Prime9999/MZ80K_SD_Pico2/KiCad/MZ80K_SD_Pico2.kicad_sch

## KiCad design KiCad/MZ80K_SD_Pico2.kicad_sch (2024-10-17)

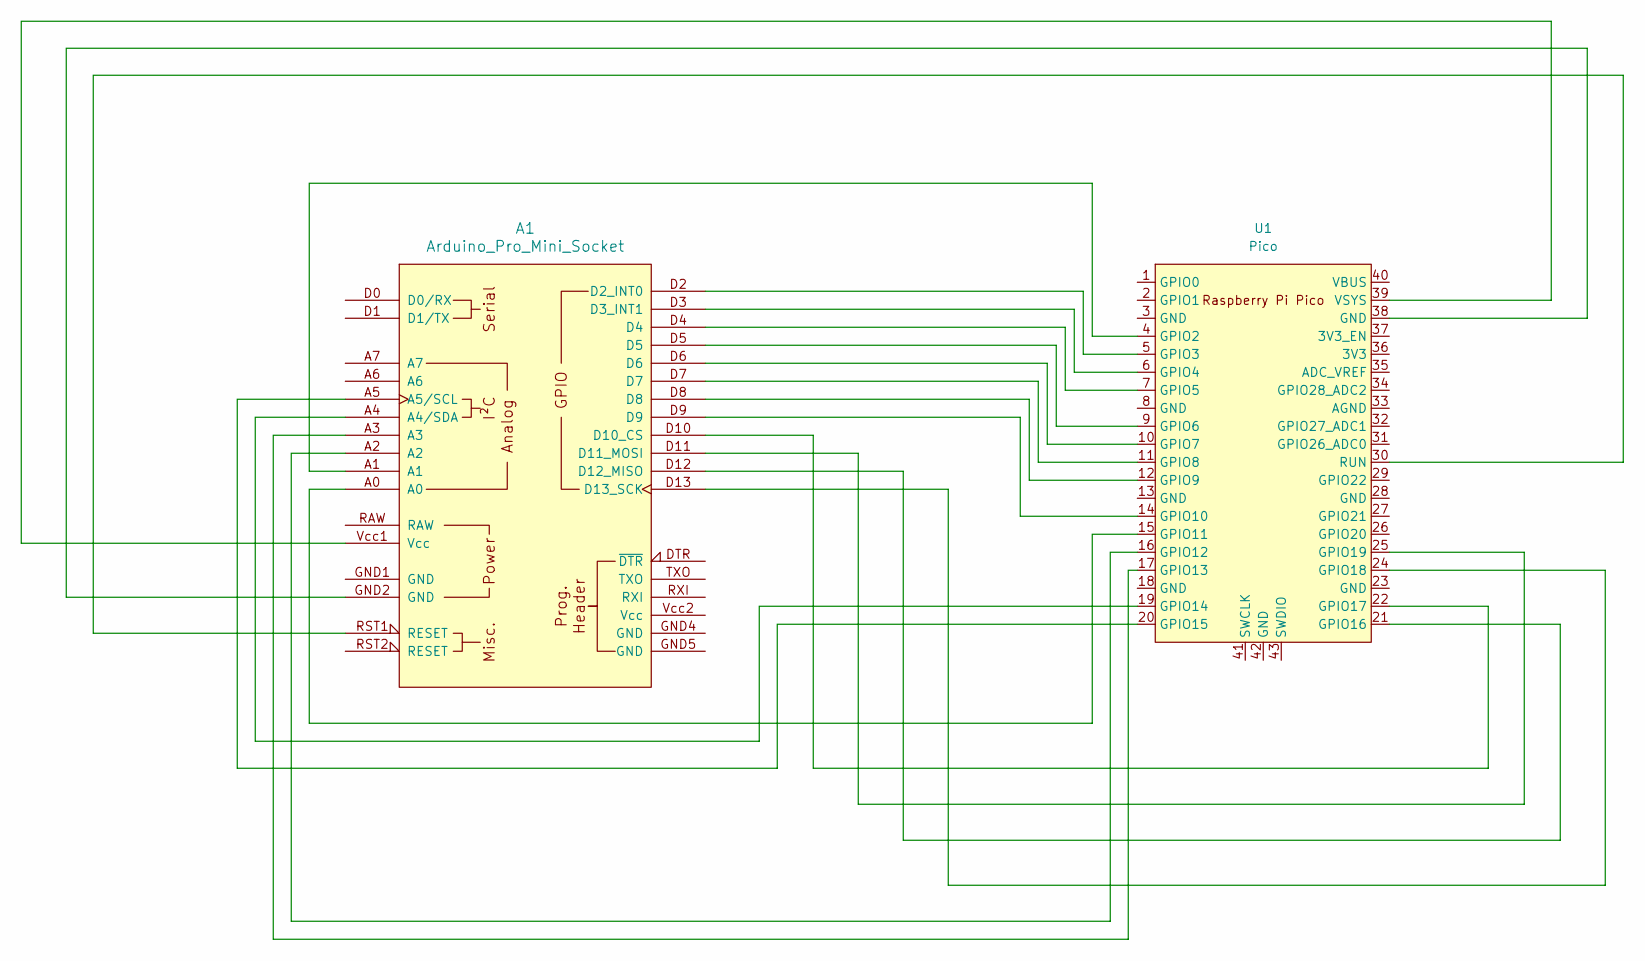
[picture p2: schematic MZ80K_SD_Pico2.kicad_sch]

Parts:
A1: Arduino_Pro_Mini_Socket; Arduino_Pro_Mini_Socket_NoSPH_2
U1: Pico; RPi_Pico_SMD_TH_2

Connections:
unnamed: A1.A0, U1.15 (GPIO11)
unnamed: A1.A1, U1.4 (GPIO2)
unnamed: A1.A2, U1.16 (GPIO12)
unnamed: A1.A3, U1.17 (GPIO13)
unnamed: A1.A4 (A4/SDA), U1.19 (GPIO14)
unnamed: A1.A5 (A5/SCL), U1.20 (GPIO15)
unnamed: A1.D2 (D2_INT0), U1.5 (GPIO3)
unnamed: A1.D3 (D3_INT1), U1.6 (GPIO4)
unnamed: A1.D4, U1.7 (GPIO5)
unnamed: A1.D5, U1.9 (GPIO6)
unnamed: A1.D6, U1.10 (GPIO7)
unnamed: A1.D7, U1.11 (GPIO8)
unnamed: A1.D8, U1.12 (GPIO9)
unnamed: A1.D9, U1.14 (GPIO10)
unnamed: A1.D10 (D10_CS), U1.22 (GPIO17)
unnamed: A1.D11 (D11_MOSI), U1.25 (GPIO19)
unnamed: A1.D12 (D12_MISO), U1.21 (GPIO16)
unnamed: A1.D13 (D13_SCK), U1.24 (GPIO18)
unnamed: A1.GND2 (GND), U1.38 (GND)
unnamed: A1.RST1 (RESET), U1.30 (RUN)
unnamed: A1.Vcc1 (Vcc), U1.39 (VSYS)
