Prime9999/MZ80K_SD_Pico2/Arduino/MZ-80K_SD_Pico2/char_table.h

/* MZ-700 Character code - UTF8 conversion table (0x70-) */

//#define SMALL_MODEL
#define MIN_ASCII_CODE ((uint8_t)0x70)
#ifdef SMALL_MODEL
#define MAX_ASCII_CODE ((uint8_t)0xbf)
#else
#define MAX_ASCII_CODE ((uint8_t)0xff)
#endif

typedef struct _ct {
  uint8_t len; // 0: cannot convert
  uint8_t bytes[3];
} char_table;

const char_table a_to_u[] PROGMEM = {
  {3, {0xe6, 0x97, 0xa5}}, // 0x70(日)
  {3, {0xe6, 0x9c, 0x88}}, // 0x71(月)
  {3, {0xe7, 0x81, 0xab}}, // 0x72(火)
  {3, {0xe6, 0xb0, 0xb4}}, // 0x73(水)
  {3, {0xe6, 0x9c, 0xA8}}, // 0x74(木)
  {3, {0xe9, 0x87, 0x91}}, // 0x75(金)
  {3, {0xe5, 0x9c, 0x9f}}, // 0x76(土)
  {3, {0xe7, 0x94, 0x9f}}, // 0x77(生)
  {3, {0xe5, 0xb9, 0xb4}}, // 0x78(年)
  {3, {0xe6, 0x99, 0x82}}, // 0x79(時)
  {3, {0xe5, 0x88, 0x86}}, // 0x7a(分)
  {3, {0xe7, 0xa7, 0x92}}, // 0x7b(秒)
  {3, {0xe5, 0x86, 0x86}}, // 0x7c(円)
  {0, {0x00, 0x00, 0x00}}, // 0x7d(￥)
  {3, {0xef, 0xbf, 0xa1}}, // 0x7e(￡)
  {0, {0x00, 0x00, 0x00}}, // 0x7f(PLAY)

  {0, {0x00, 0x00, 0x00}}, // 0x80(↓)
  {3, {0xef, 0xbd, 0xa1}}, // 0x81(｡)
  {3, {0xef, 0xbd, 0xa2}}, // 0x82(｢)
  {3, {0xef, 0xbd, 0xa3}}, // 0x83(｣)
  {3, {0xef, 0xbd, 0xa4}}, // 0x84(､)
  {3, {0xef, 0xbd, 0xa5}}, // 0x85(･)
  {3, {0xef, 0xbd, 0xa6}}, // 0x86(ｦ)
  {3, {0xef, 0xbd, 0xa7}}, // 0x87(ｧ)
  {3, {0xef, 0xbd, 0xa8}}, // 0x88(ｨ)
  {3, {0xef, 0xbd, 0xa9}}, // 0x89(ｩ)
  {3, {0xef, 0xbd, 0xaa}}, // 0x8a(ｪ)
  {3, {0xef, 0xbd, 0xab}}, // 0x8b(ｫ)
  {3, {0xef, 0xbd, 0xac}}, // 0x8c(ｬ)
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
  {3, {0xe2, 0x97, 0xa3}}, // 0xe9(◣)
  {3, {0xe2, 0x95, 0xb0}}, // 0xea(╰)
  {3, {0xe2, 0x95, 0xaf}}, // 0xeb(╯)
  {0, {0x00, 0x00, 0x00}}, // 0xec(??)
  {3, {0xe2, 0x95, 0xb2}}, // 0xed(╲)
  {3, {0xe2, 0x95, 0xb1}}, // 0xee(╱)
  {0, {0x00, 0x00, 0x00}}, // 0xef(??)

  {0, {0x00, 0x00, 0x00}}, // 0xf0(??)
  {3, {0xe2, 0x97, 0x8f}}, // 0xf1(●)
  {0, {0x00, 0x00, 0x00}}, // 0xf2(??)
  {3, {0xe2, 0x99, 0xa5}}, // 0xf3(♥)
  {0, {0x00, 0x00, 0x00}}, // 0xf4(??)
  {3, {0xe2, 0x97, 0xa2}}, // 0xf5(◢)
  {3, {0xe2, 0x95, 0xb3}}, // 0xf6(╳)
  {3, {0xe2, 0x97, 0x8b}}, // 0xf7(○)
  {3, {0xe2, 0x99, 0xa3}}, // 0xf8(♣)
  {0, {0x00, 0x00, 0x00}}, // 0xf9(??)
  {3, {0xe2, 0x99, 0xa6}}, // 0xfa(♦)
  {3, {0xe2, 0x94, 0xbc}}, // 0xfb(┼)
  {0, {0x00, 0x00, 0x00}}, // 0xfc(??)
  {3, {0xe2, 0x94, 0x82}}, // 0xfd(│)
  {3, {0xe2, 0x97, 0xa5}}, // 0xfe(◥)
  {2, {0xcf, 0x80, 0x00}}, // 0xff(π)
#endif
};
