Prime9999/MZ80K_SD_Pico2/Arduino/PC-8001_SD_Pico2/char_table.h

/* PC-8001 Character code - UTF8 conversion table (0x80-) */

#define MIN_ASCII_CODE ((uint8_t)0x80)
#define MAX_ASCII_CODE ((uint8_t)0xff)

typedef struct _ct {
  uint8_t len; // 0: cannot convert
  char bytes[3];
} char_table;

const char_table a_to_u[] PROGMEM = {
  {3, {0xe2, 0x96, 0x81}}, // 0x80(▁)
  {3, {0xe2, 0x96, 0x82}}, // 0x81(▂)
  {3, {0xe2, 0x96, 0x83}}, // 0x82(▃)
  {3, {0xe2, 0x96, 0x84}}, // 0x83(▄)
  {3, {0xe2, 0x96, 0x85}}, // 0x84(▅)
  {3, {0xe2, 0x96, 0x86}}, // 0x85(▆)
  {3, {0xe2, 0x96, 0x87}}, // 0x86(▇)
  {3, {0xe2, 0x96, 0x88}}, // 0x87(█)
  {3, {0xe2, 0x96, 0x8f}}, // 0x88(▏)
  {3, {0xe2, 0x96, 0x8e}}, // 0x89(▎)
  {3, {0xe2, 0x96, 0x8d}}, // 0x8a(▍)
  {3, {0xe2, 0x96, 0x8c}}, // 0x8b(▌)
  {3, {0xe2, 0x96, 0x8b}}, // 0x8c(▋)
  {3, {0xe2, 0x96, 0x8a}}, // 0x8d(▊)
  {3, {0xe2, 0x96, 0x89}}, // 0x8e(▉)
  {3, {0xe2, 0x94, 0xbc}}, // 0x8f(┼)

  {3, {0xe2, 0x94, 0xb4}}, // 0x90(┴)
  {3, {0xe2, 0x94, 0xac}}, // 0x91(┬)
  {3, {0xe2, 0x94, 0xa4}}, // 0x92(┤)
  {3, {0xe2, 0x94, 0x9c}}, // 0x93(├)
  {3, {0xe2, 0x96, 0x94}}, // 0x94(▔)
  {3, {0xe2, 0x94, 0x80}}, // 0x95(─)
  {3, {0xe2, 0x94, 0x82}}, // 0x96(│)
  {3, {0xe2, 0x96, 0x95}}, // 0x97(▕)
  {3, {0xe2, 0x94, 0x8c}}, // 0x98(┌)
  {3, {0xe2, 0x94, 0x90}}, // 0x99(┐)
  {3, {0xe2, 0x94, 0x94}}, // 0x9a(└)
  {3, {0xe2, 0x94, 0x98}}, // 0x9b(┘)
  {3, {0xe2, 0x95, 0xad}}, // 0x9c(╭)
  {3, {0xe2, 0x95, 0xae}}, // 0x9d(╮)
  {3, {0xe2, 0x95, 0xb0}}, // 0x9e(╰)
  {3, {0xe2, 0x95, 0xaf}}, // 0x9f(╯)

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
  {0, {0x00, 0x00, 0x00}}, // 0xf9()
  {0, {0x00, 0x00, 0x00}}, // 0xfa()
  {0, {0x00, 0x00, 0x00}}, // 0xfb()
  {0, {0x00, 0x00, 0x00}}, // 0xfc()
  {0, {0x00, 0x00, 0x00}}, // 0xfd()
  {0, {0x00, 0x00, 0x00}}, // 0xfe()
  {0, {0x00, 0x00, 0x00}}, // 0xff()
};
